42Bastian/EPROMEmu/src/teensy/ubll.h

const uint8_t uBLL[] = {
   0xff,0xbe,0xc5,0x43,0x3d,0x7c,0x15,0xb0,0xdc,0xc7,0x74,0x28,0x41,0x4b,0xd9,0x81,
   0x81,0xef,0x4f,0x1e,0x5c,0x30,0x28,0x73,0x1d,0xe5,0xf5,0x87,0xa7,0x1f,0x60,0x19,
   0x02,0x70,0xe0,0x2e,0x82,0x06,0x38,0x89,0x7f,0xb2,0x05,0xc1,0x50,0x59,0x5f,0xd2,
   0xb3,0x47,0x7c,0x2a,0xcd,0xa2,0x0b,0xbc,0x81,0x01,0xbd,0x8d,0x01,0x99,0x00,0xfc,
   0xca,0x10,0xf4,0xa2,0x06,0xbc,0x73,0x01,0xbd,0x7a,0x01,0x99,0x00,0xfd,0xca,0x10,
   0xf4,0xad,0xb0,0xfc,0xd0,0x08,0xce,0xa0,0xfd,0xa9,0x10,0x8d,0x9c,0xfd,0x2c,0x8c,
   0xfd,0x50,0xfb,0xad,0x8d,0xfd,0xc9,0x81,0xd0,0xf4,0x2c,0x8c,0xfd,0x50,0xfb,0xad,
   0x8d,0xfd,0xc9,0x50,0xd0,0xe8,0xa0,0x04,0x2c,0x8c,0xfd,0x50,0xfb,0xad,0x8d,0xfd,
   0x99,0xff,0xff,0x99,0x03,0x00,0x88,0xd0,0xef,0xaa,0xe8,0xd0,0x07,0xe6,0x01,0xd0,
   0x03,0x6c,0x02,0x00,0x2c,0x8c,0xfd,0x50,0xfb,0xad,0x8d,0xfd,0x91,0x06,0x8d,0xb0,
   0xfd,0xc8,0xd0,0xe6,0xe6,0x07,0x80,0xe2,0x10,0x11,0x8c,0x91,0x90,0xb3,0xa0,0x01,
   0x18,0x1d,0x00,0x00,0x0f,0x00,0x91,0x11,0x10,0x09,0x08,0x04,0x06,0x28,0x2a,0x83,
   0x92,0x90,0x01,0x01,0x98,0x20,0x00,0x00,0x00,0x7f,0x7f,0xf3,0x00,0x01,0x90,0x00,
   0x00,0x00,0xa8,0x01,0x3b,0x00,0x30,0x00,0x00,0x01,0x00,0x02,0x03,0x07,0xe3,0x7d,
   0x81,0xbc,0x61,0x80,0x07,0xf3,0x61,0x81,0xb3,0x61,0x80,0x07,0xdb,0x78,0xdb,0x3c,
   0x61,0x80,0x07,0xcf,0x60,0xdb,0x33,0x61,0x80,0x07,0xc7,0x7c,0x7e,0x3c,0x7d,0xf0,
   0
};
